ajithvasudevan/TimerClock/ClockTimer2.sch

## KiCad design ClockTimer2.sch (2020-07-01)

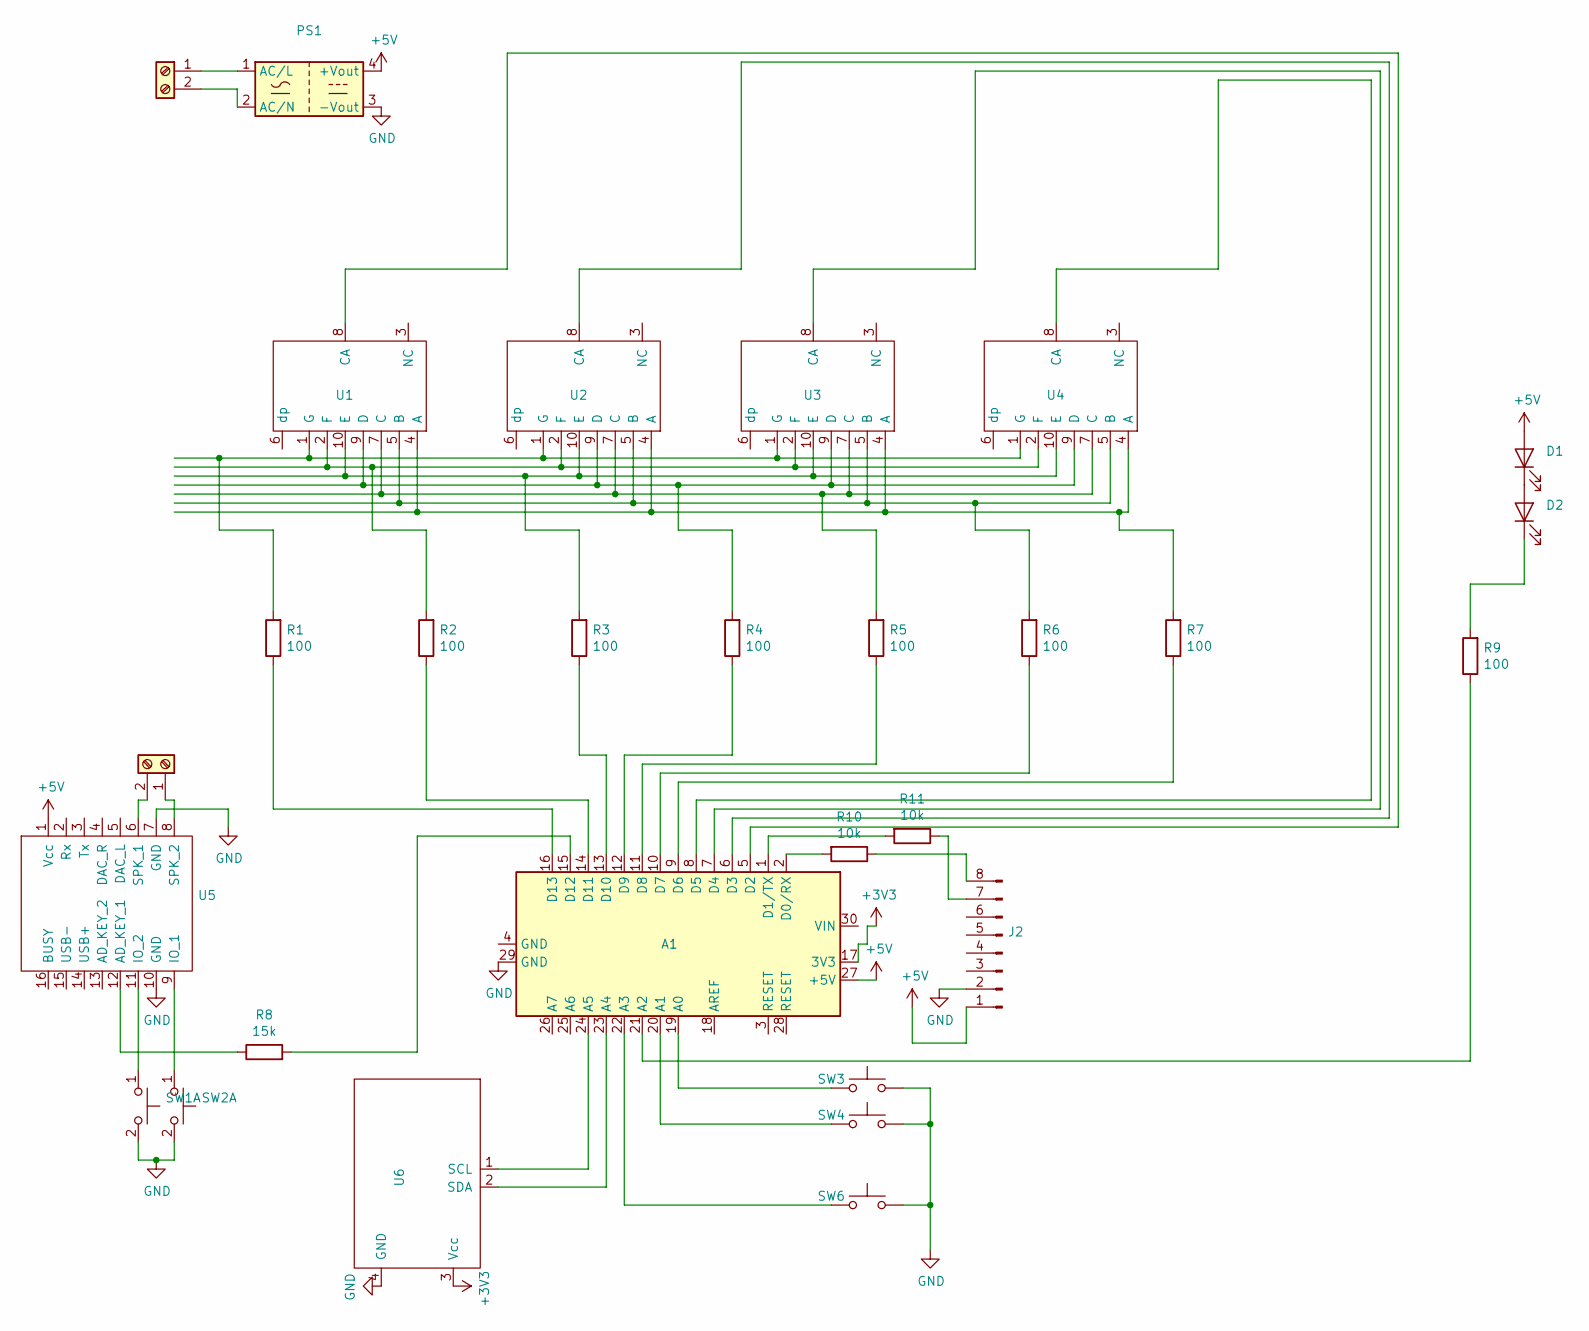
[picture p3: schematic ClockTimer2.sch]

Parts:
A1: Arduino_Nano
D1, D2: LED_D3.0mm
J1, J3: TerminalBlock_bornier-2_P5.08mm
J2: PinHeader_1x08_P2.54mm_Vertical
PS1: Converter_ACDC_HiLink_HLK-PMxx
R1, R2, R3, R4, R5, R6, R7, R9: 100; R_Axial_DIN0207_L6.3mm_D2.5mm_P10.16mm_Horizontal
R8: 15k; R_Axial_DIN0207_L6.3mm_D2.5mm_P10.16mm_Horizontal
R10, R11: 10k; R_Axial_DIN0207_L6.3mm_D2.5mm_P10.16mm_Horizontal
SW1, SW2: SW_PUSH_6mm_H5mm
SW3, SW4, SW6: SW_PUSH_6mm_H8mm
U1, U2, U3, U4: 7-segment-CA-1-inch
U5: DF_Player_Mini
U6: DS3231_RTC

Connections:
+3V3: A1.17 (3V3), U6.3 (Vcc)
+5V: A1.27 (+5V), D1.2 (A), J2.1, PS1.4 (+Vout), U5.1 (Vcc)
GND: A1.29 (GND), J2.2, PS1.3 (-Vout), SW1.2 (D), SW2.2 (D), SW3.2, SW4.2, SW6.2, U5.7 (GND), U5.10 (GND), U6.4 (GND)
unnamed: A1.1 (D1/TX), R11.2
unnamed: A1.2 (D0/RX), R10.2
unnamed: A1.5 (D2), U1.8 (CA)
unnamed: A1.6 (D3), U2.8 (CA)
unnamed: A1.7 (D4), U3.8 (CA)
unnamed: A1.8 (D5), U4.8 (CA)
unnamed: A1.9 (D6), R7.1
unnamed: A1.10 (D7), R6.1
unnamed: A1.11 (D8), R5.1
unnamed: A1.12 (D9), R4.1
unnamed: A1.13 (D10), R3.1
unnamed: A1.14 (D11), R2.1
unnamed: A1.15 (D12), R8.2
unnamed: A1.16 (D13), R1.1
unnamed: A1.19 (A0), SW3.1
unnamed: A1.20 (A1), SW4.1
unnamed: A1.21 (A2), R9.1
unnamed: A1.22 (A3), SW6.1
unnamed: A1.23 (A4), U6.2 (SDA)
unnamed: A1.24 (A5), U6.1 (SCL)
unnamed: D1.1 (K), D2.2 (A)
unnamed: D2.1 (K), R9.2
unnamed: J1.1, PS1.1 (AC/L)
unnamed: J1.2, PS1.2 (AC/N)
unnamed: J2.7, R11.1
unnamed: J2.8, R10.1
unnamed: J3.1, U5.8 (SPK_2)
unnamed: J3.2, U5.6 (SPK_1)
unnamed: R1.2, U1.1 (G), U2.1 (G), U3.1 (G), U4.1 (G)
unnamed: R2.2, U1.2 (F), U2.2 (F), U3.2 (F), U4.2 (F)
unnamed: R3.2, U1.10 (E), U2.10 (E), U3.10 (E), U4.10 (E)
unnamed: R4.2, U1.9 (D), U2.9 (D), U3.9 (D), U4.9 (D)
unnamed: R5.2, U1.7 (C), U2.7 (C), U3.7 (C), U4.7 (C)
unnamed: R6.2, U1.5 (B), U2.5 (B), U3.5 (B), U4.5 (B)
unnamed: R7.2, U1.4 (A), U2.4 (A), U3.4 (A), U4.4 (A)
unnamed: R8.1, U5.12 (AD_KEY_1)
unnamed: SW1.1 (C), U5.11 (IO_2)
unnamed: SW2.1 (C), U5.9 (IO_1)
